Ogbonna-Joseph/1KVA-SINE-WAVE-POWER-INVERTER/Images/componentselect.png

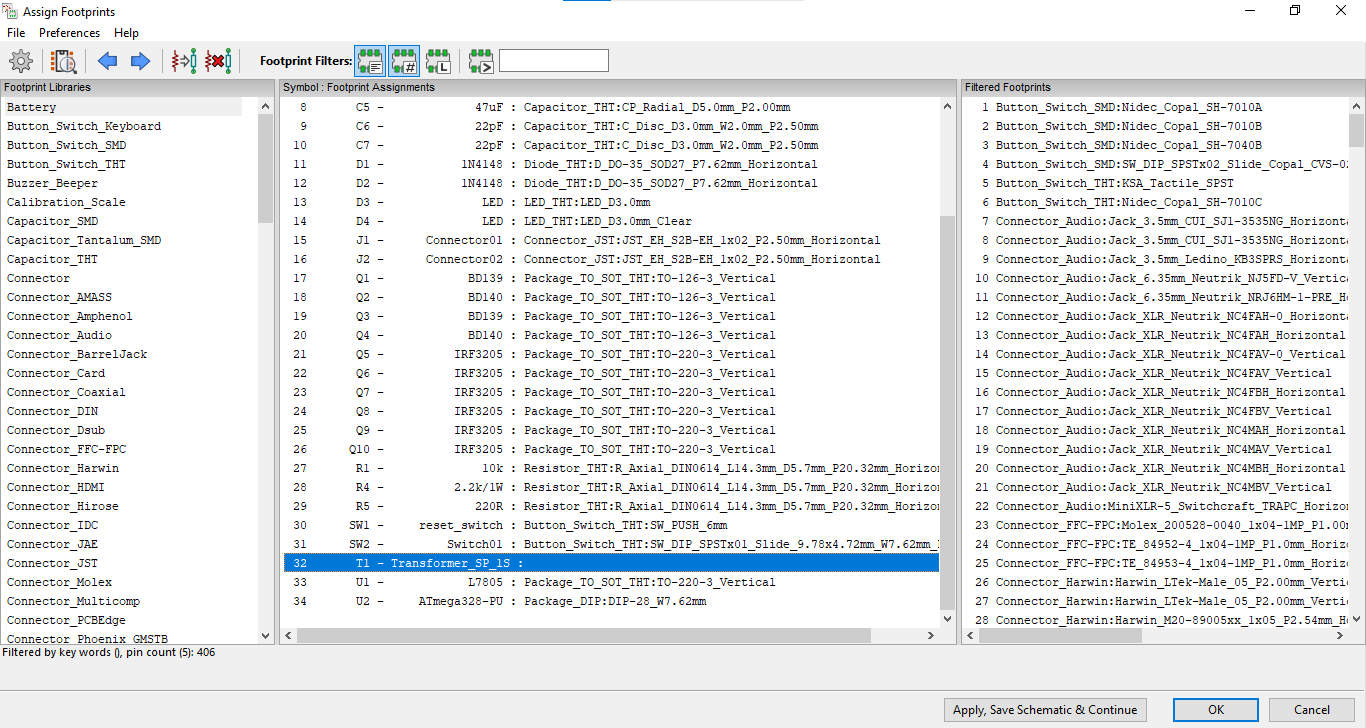
Images/componentselect.png
