Ogbonna-Joseph/1KVA-SINE-WAVE-POWER-INVERTER/Images/Inverter02.png

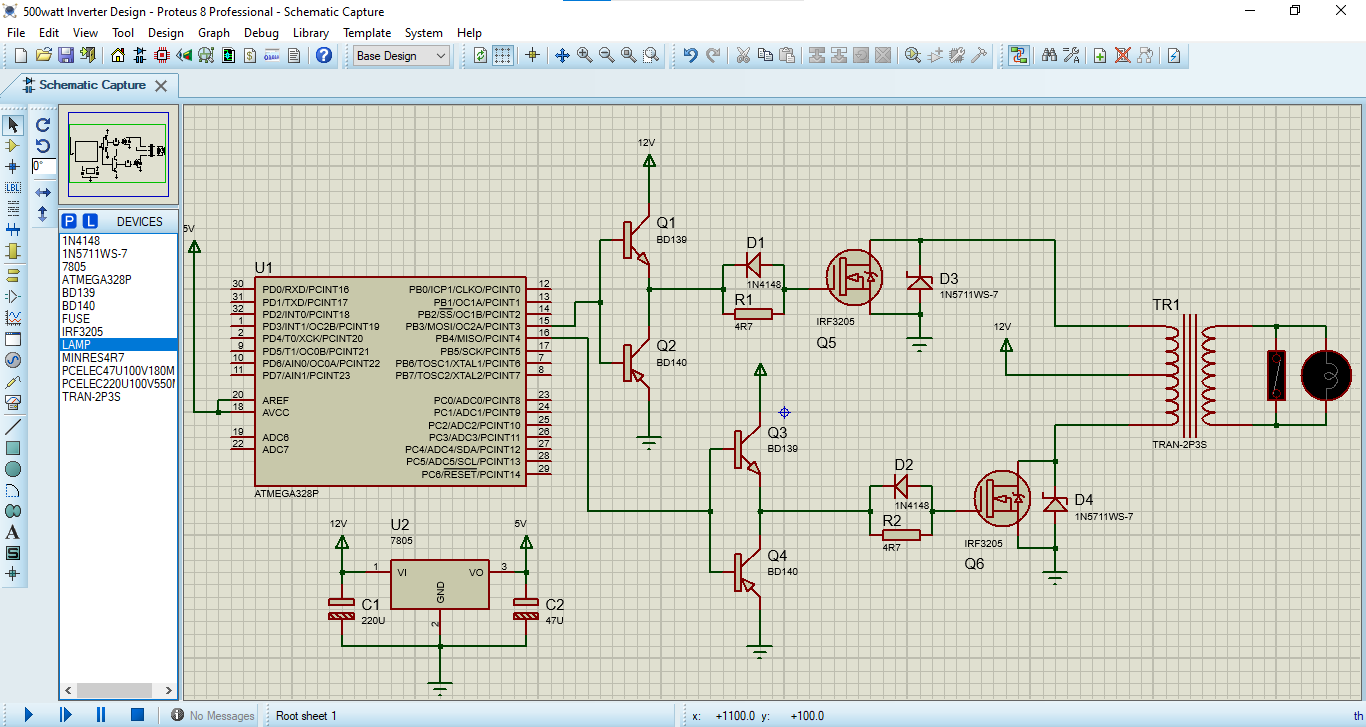
Images/Inverter02.png
