Ogbonna-Joseph/1KVA-SINE-WAVE-POWER-INVERTER/Images/Inverter03.png

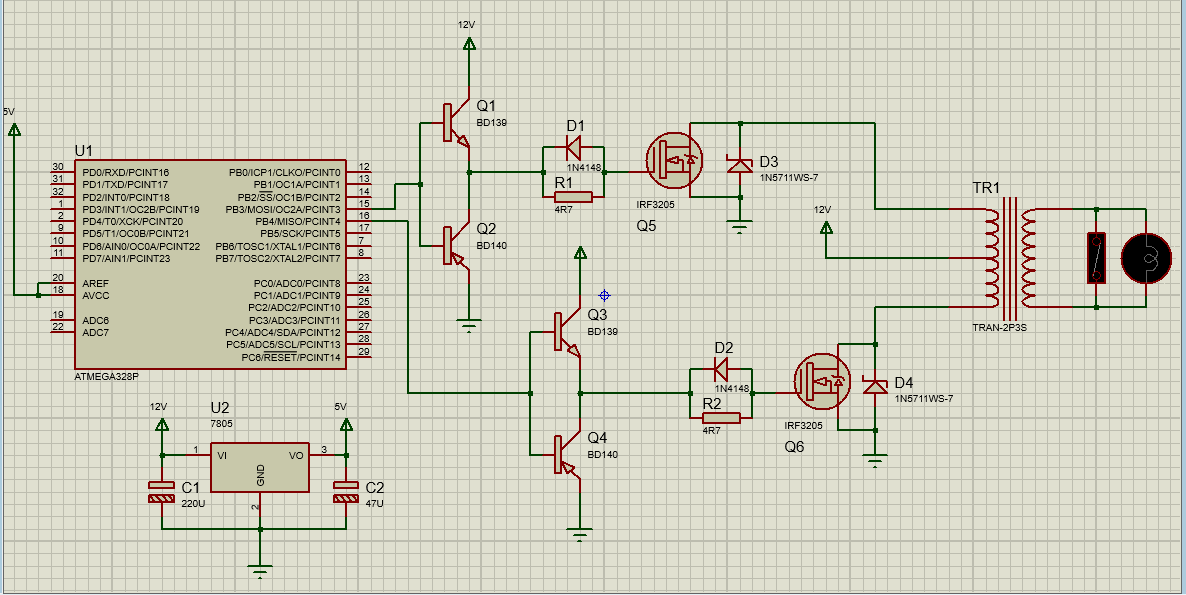
Images/Inverter03.png
