Ogbonna-Joseph/1KVA-SINE-WAVE-POWER-INVERTER/Images/InverterUPD.png

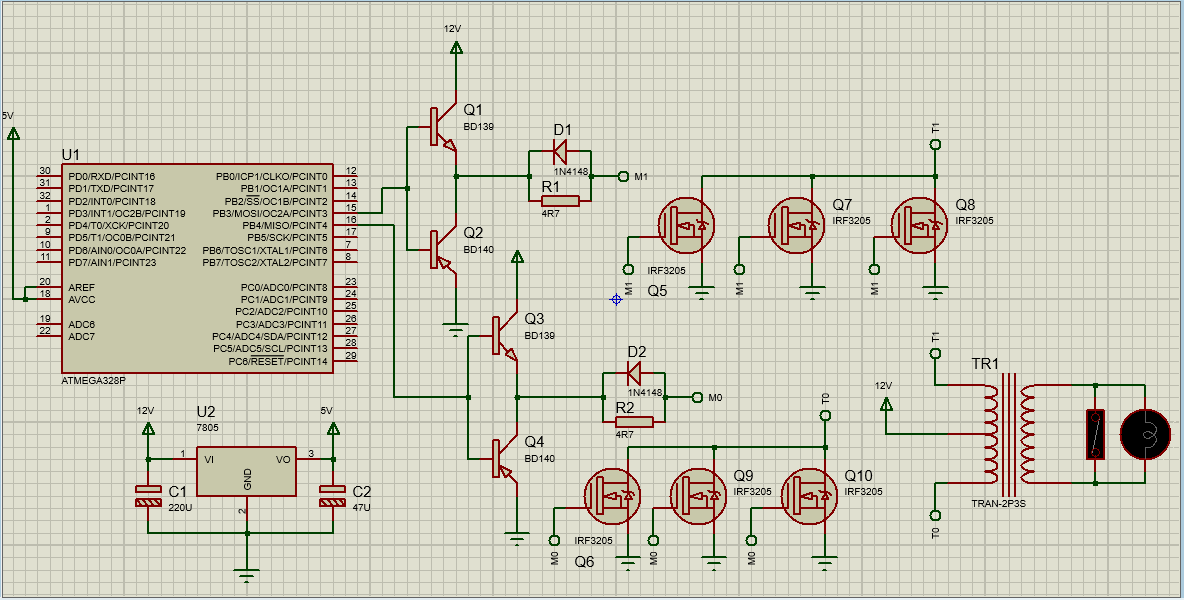
Images/InverterUPD.png
