Ogbonna-Joseph/1KVA-SINE-WAVE-POWER-INVERTER/Images/pcb0001.png

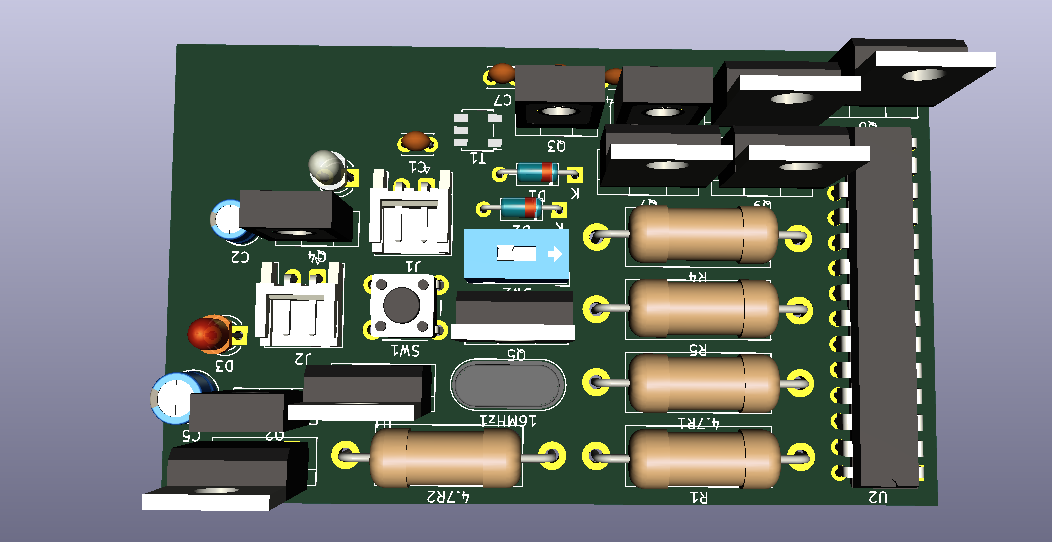
Images/pcb0001.png
