Ogbonna-Joseph/1KVA-SINE-WAVE-POWER-INVERTER/Images/PCBBACK.png

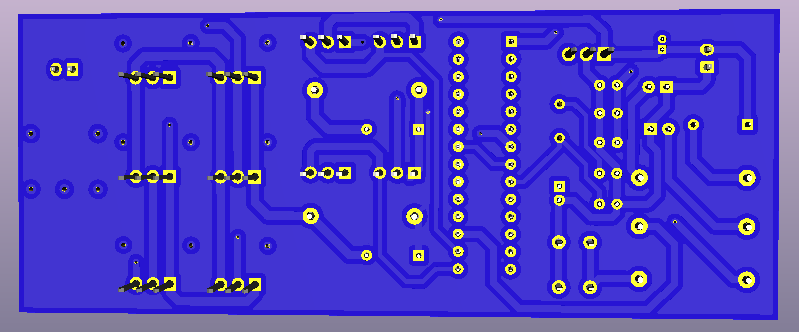
Images/PCBBACK.png
