Ogbonna-Joseph/1KVA-SINE-WAVE-POWER-INVERTER/Images/PCBBBBB.png

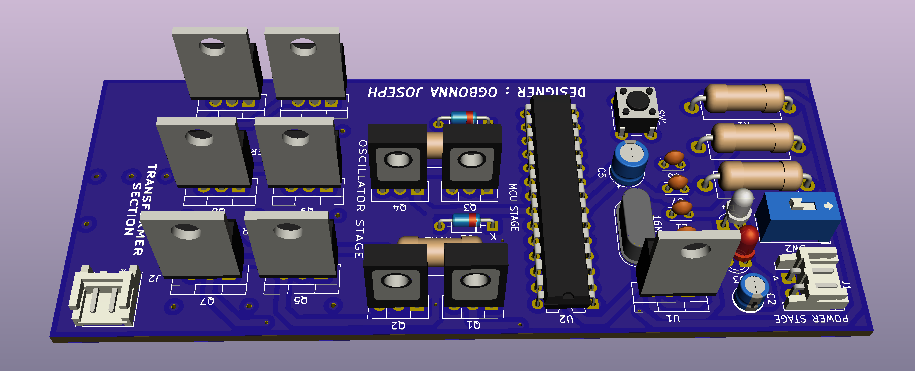
Images/PCBBBBB.png
