Ogbonna-Joseph/1KVA-SINE-WAVE-POWER-INVERTER/Images/pcbway002.png

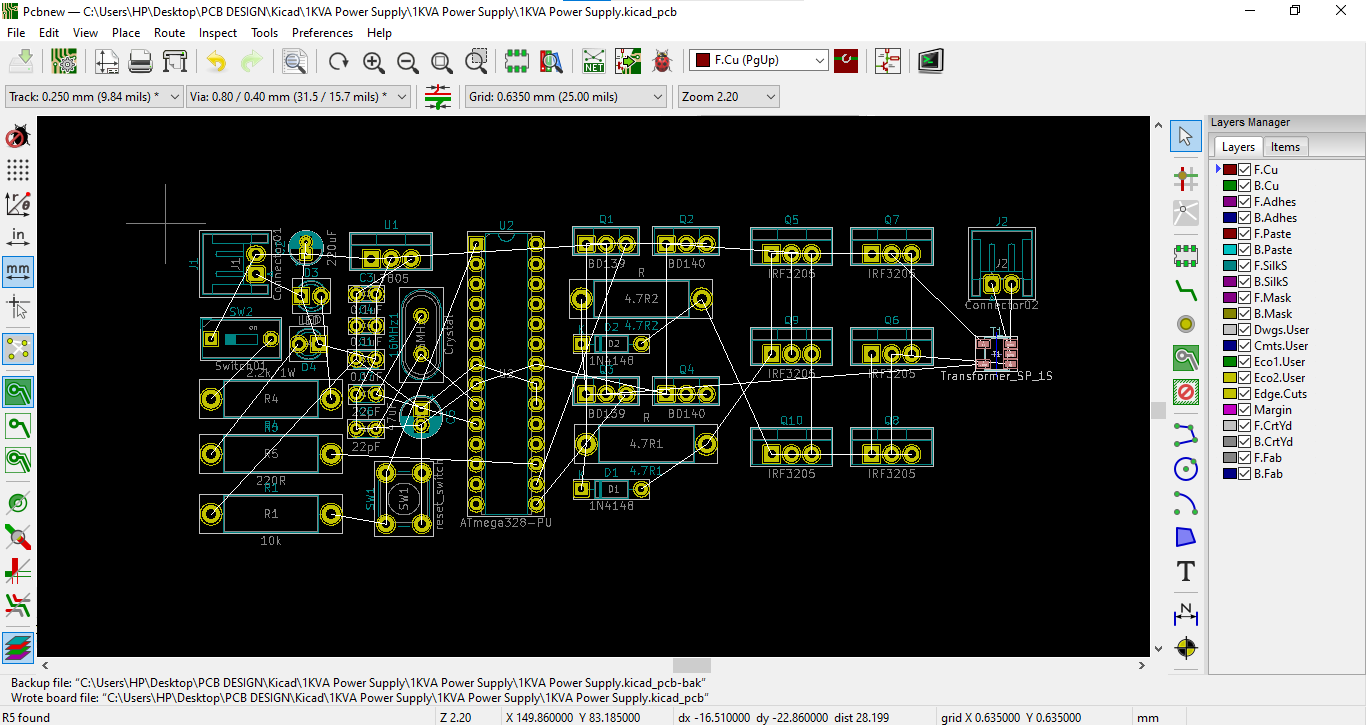
Images/pcbway002.png
