Ogbonna-Joseph/1KVA-SINE-WAVE-POWER-INVERTER/Images/pcbway003.png

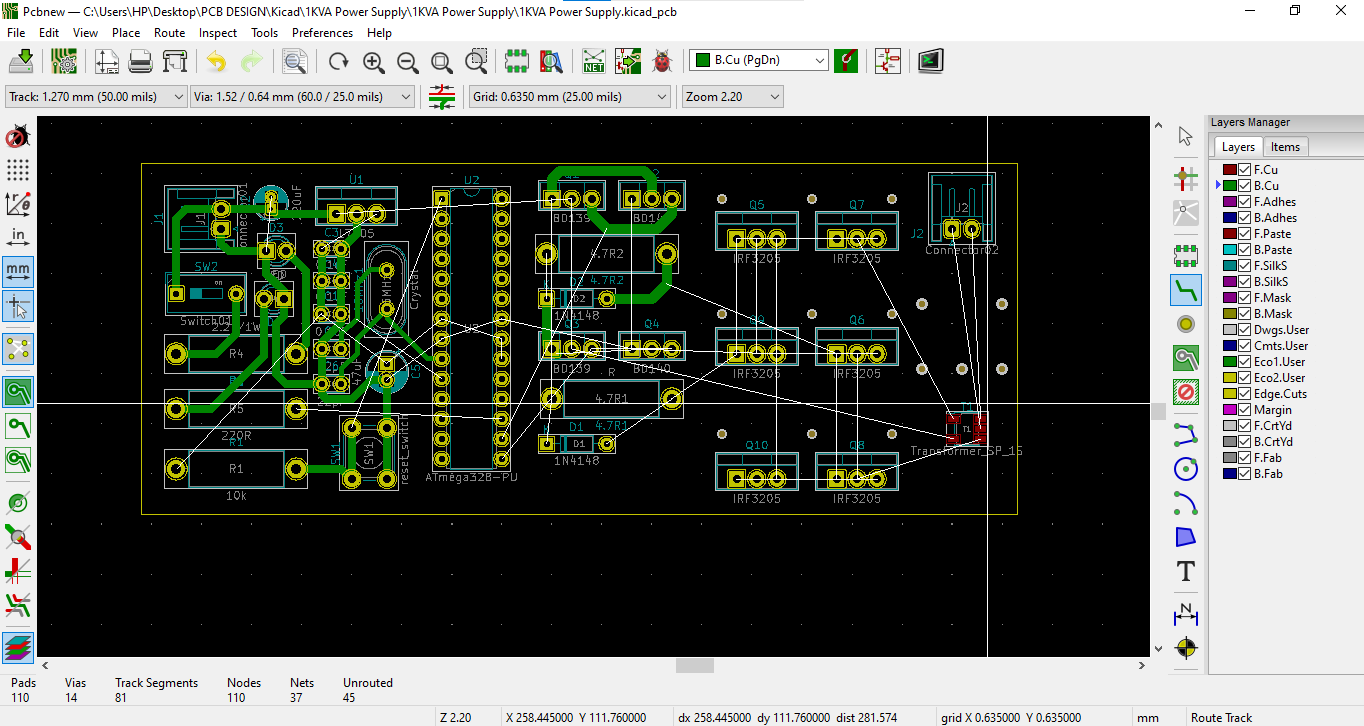
Images/pcbway003.png
