Ogbonna-Joseph/1KVA-SINE-WAVE-POWER-INVERTER/Images/PCBWAY0123.png

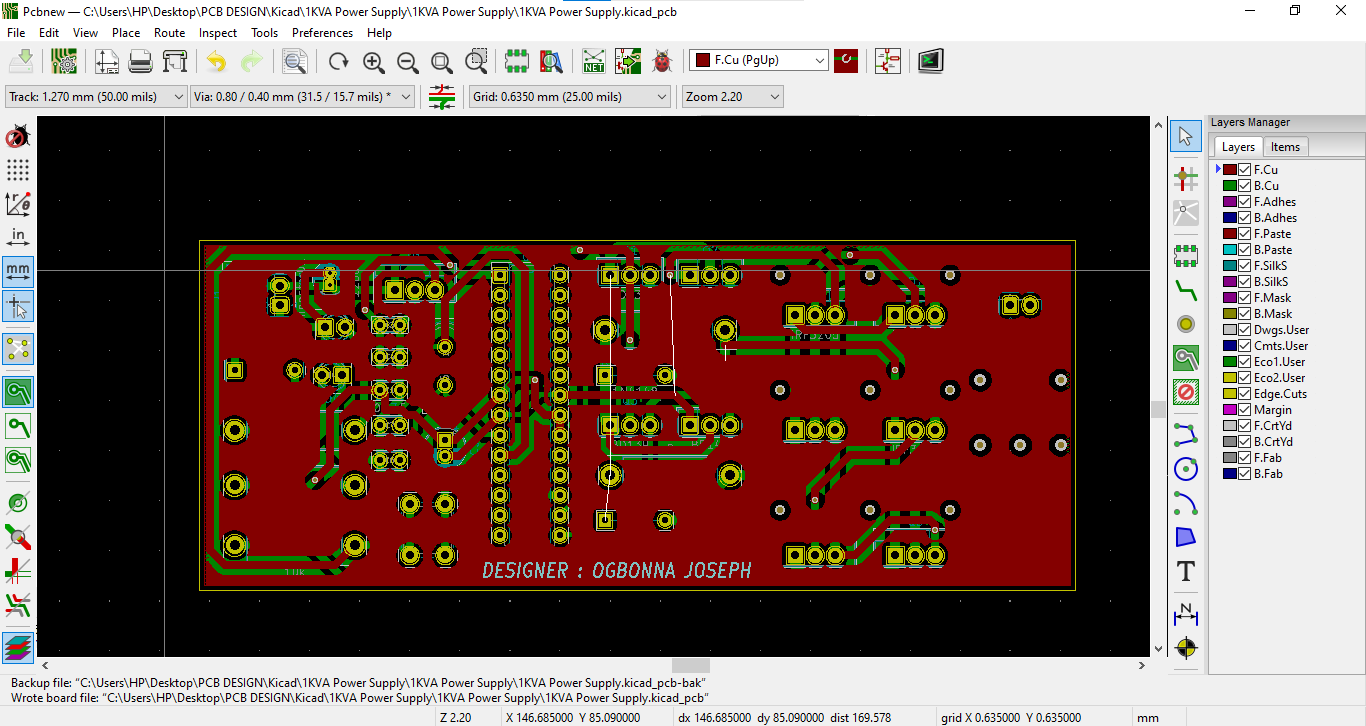
Images/PCBWAY0123.png
